DIYSynthMNL/Multi-Angle-Eurorack-1-Row-Case/images/Built 1.jpg

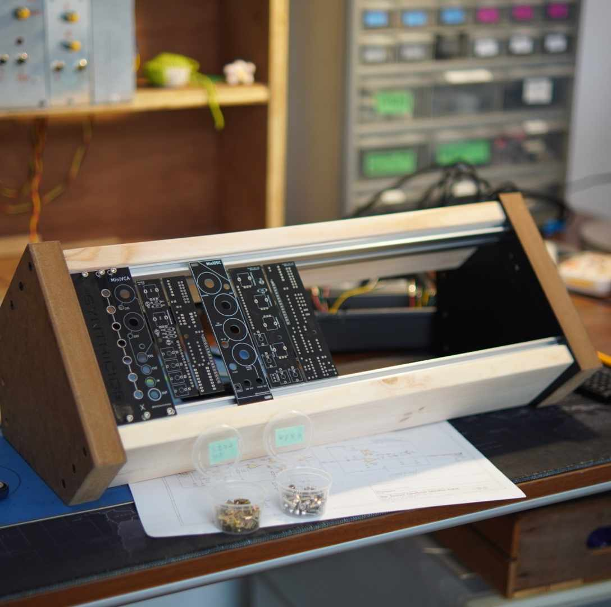
images/Built 1.jpg
