DIYSynthMNL/Multi-Angle-Eurorack-1-Row-Case/images/Built 4.jpg

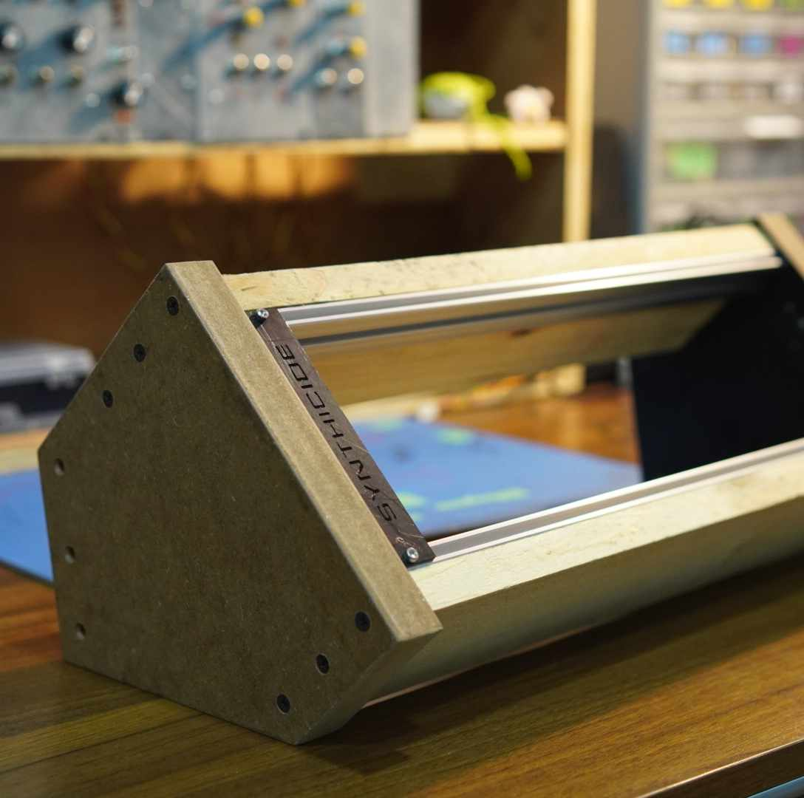
images/Built 4.jpg
