DIYSynthMNL/Multi-Angle-Eurorack-1-Row-Case/images/Built 5.jpg

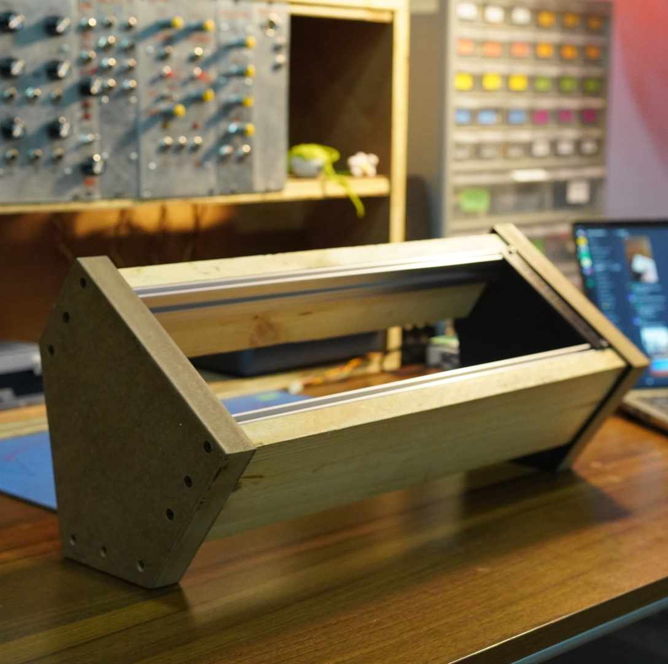
images/Built 5.jpg
