DIYSynthMNL/Multi-Angle-Eurorack-1-Row-Case/images/Built 6.jpg

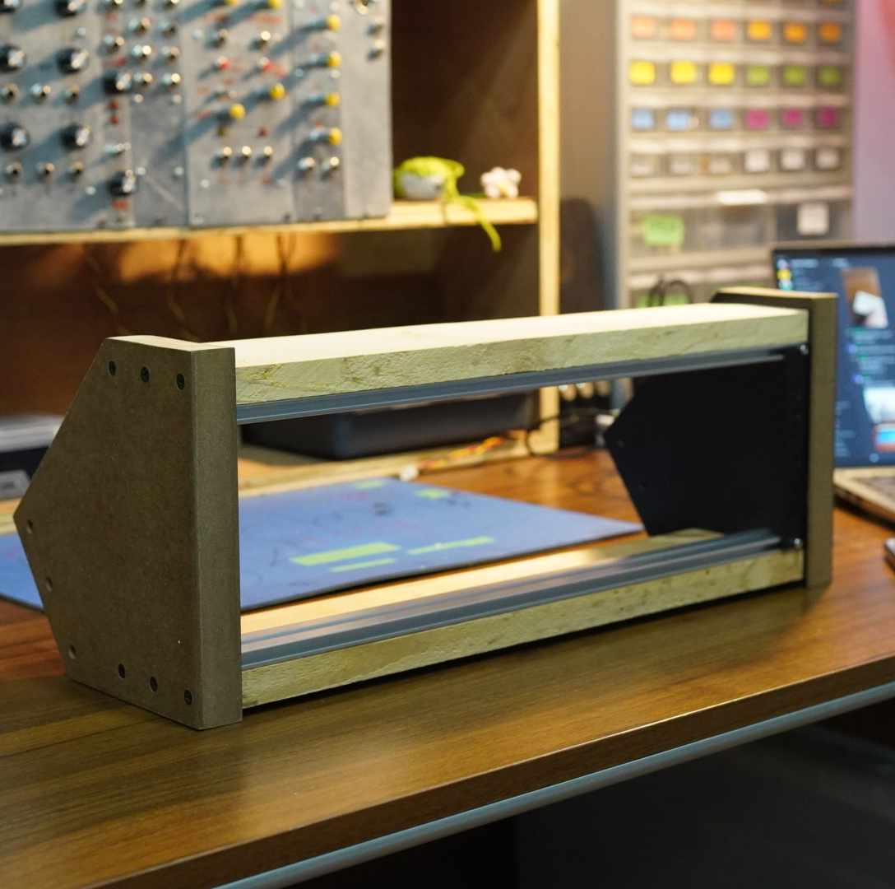
images/Built 6.jpg
