DIYSynthMNL/Multi-Angle-Eurorack-1-Row-Case/images/Untitled 1.png

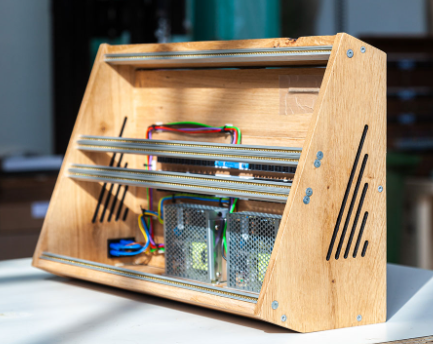
images/Untitled 1.png
