DIYSynthMNL/Multi-Angle-Eurorack-1-Row-Case/images/Untitled 3.png

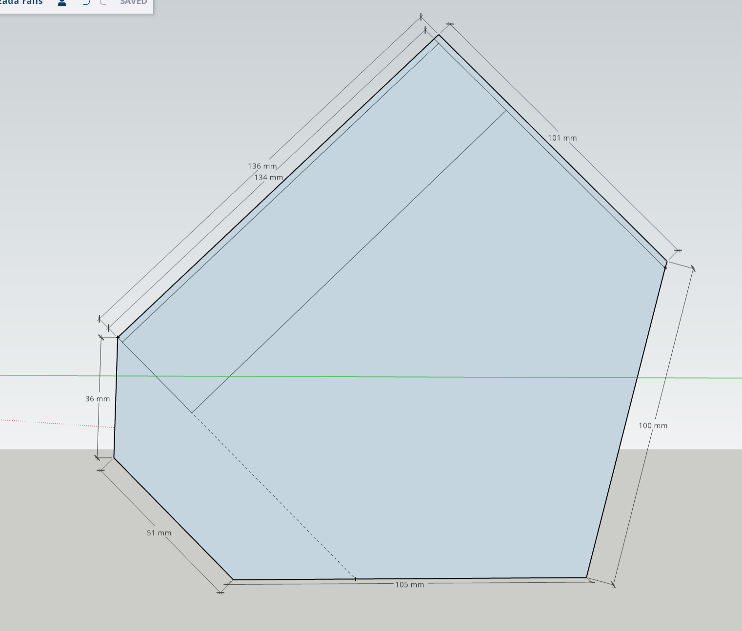
images/Untitled 3.png
