DIYSynthMNL/Multi-Angle-Eurorack-1-Row-Case/images/Untitled 6.png

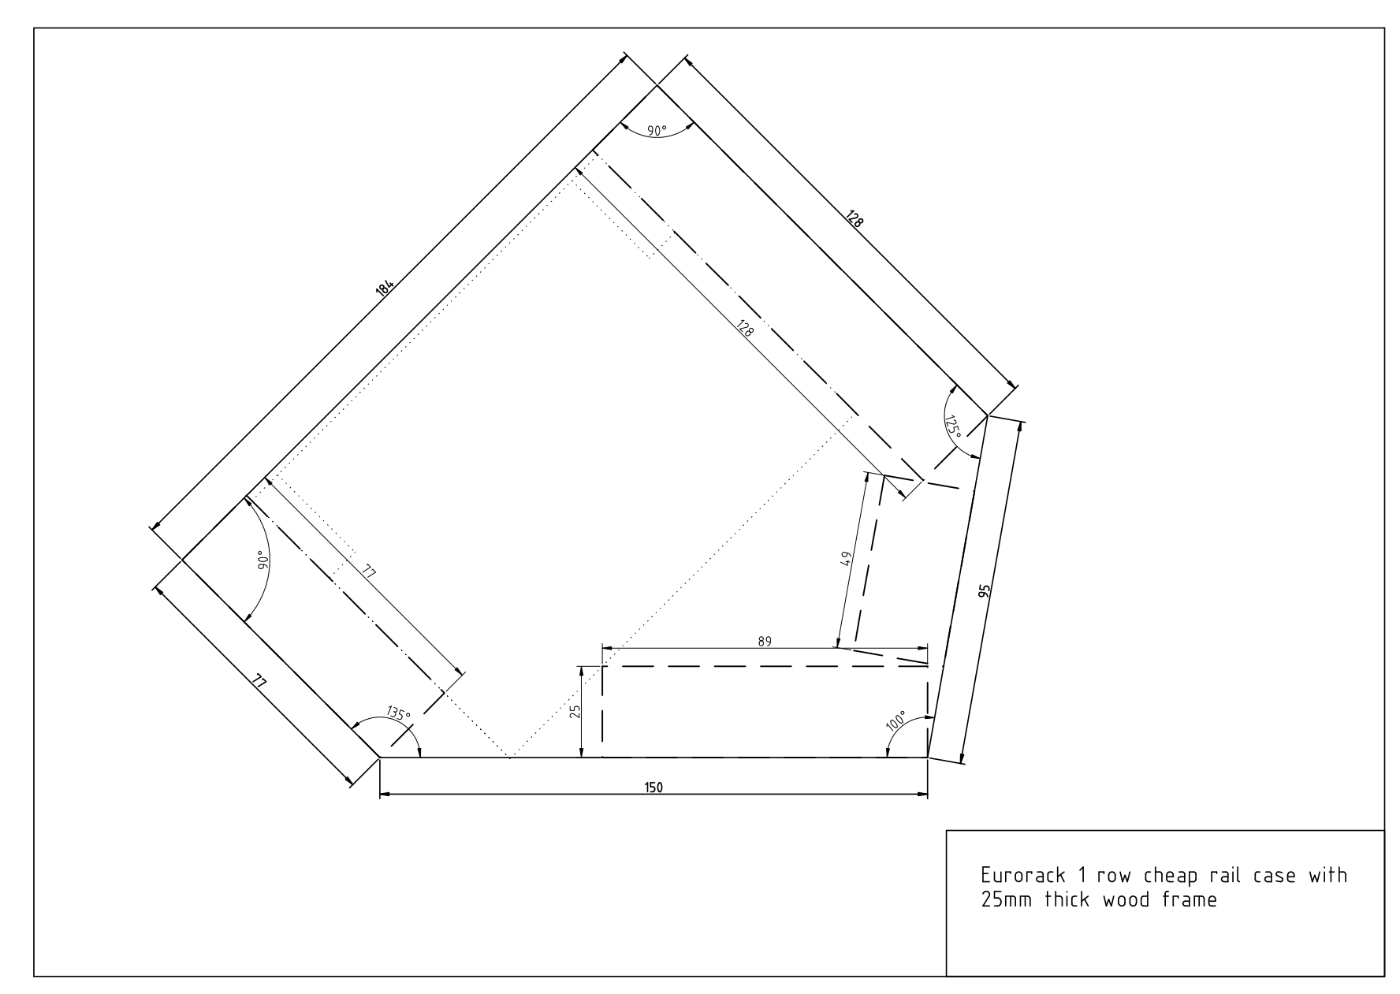
images/Untitled 6.png
