DIYSynthMNL/Multi-Angle-Eurorack-1-Row-Case/images/Untitled 8.png

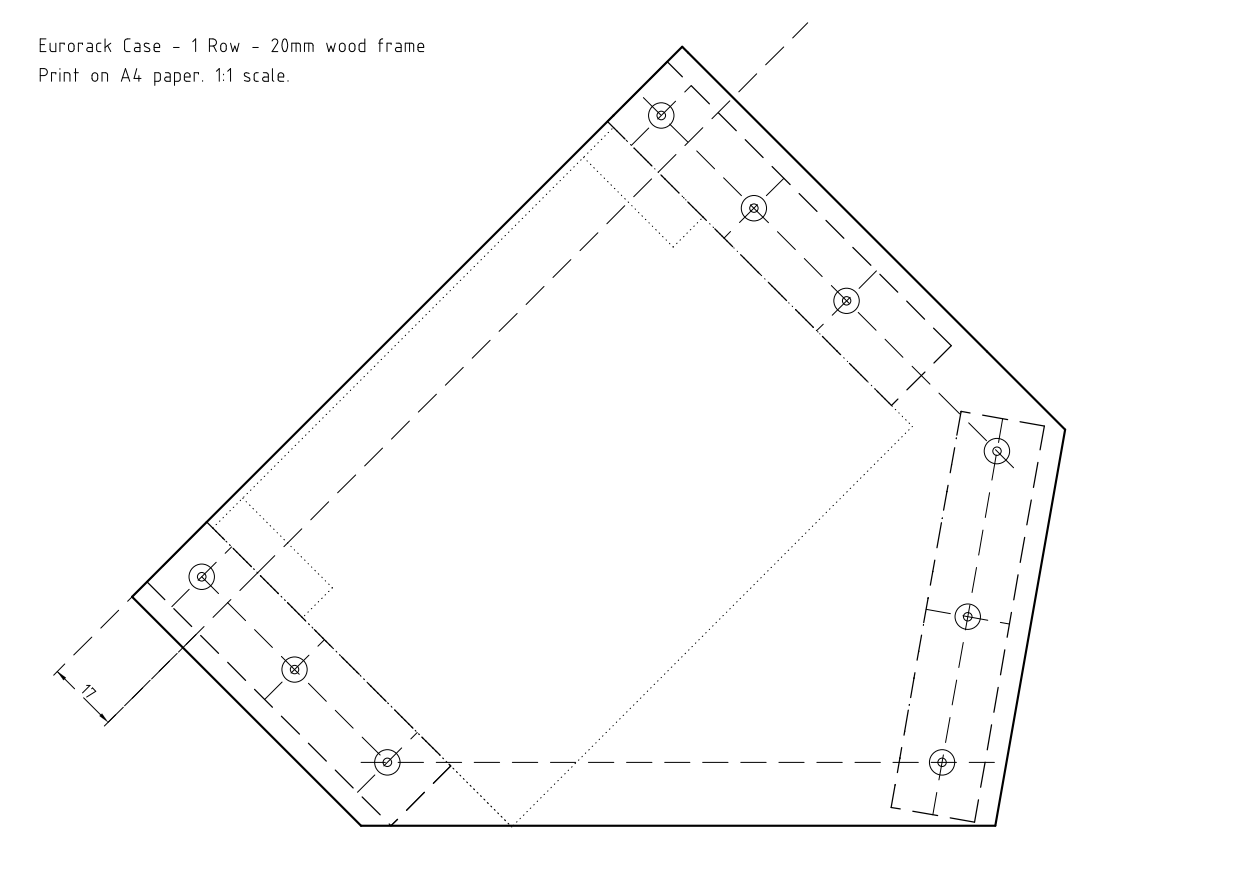
images/Untitled 8.png
