DIYSynthMNL/Multi-Angle-Eurorack-1-Row-Case/images/Untitled.png

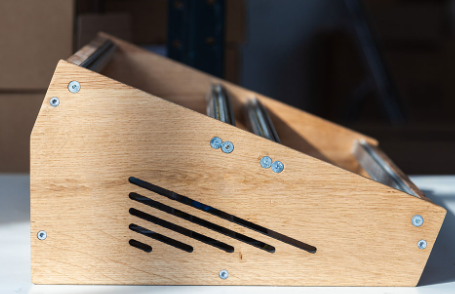
images/Untitled.png
