DIYSynthMNL/Multi-Angle-Eurorack-1-Row-Case/photos/with-modules-detail.jpg

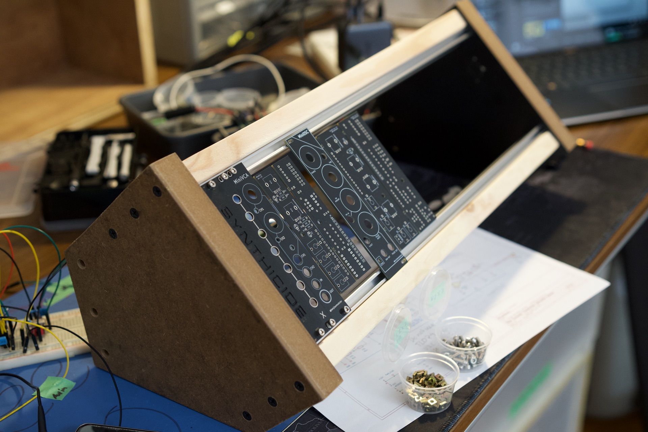
photos/with-modules-detail.jpg
