DIYSynthMNL/Multi-Angle-Eurorack-1-Row-Case/photos/with-modules.jpg

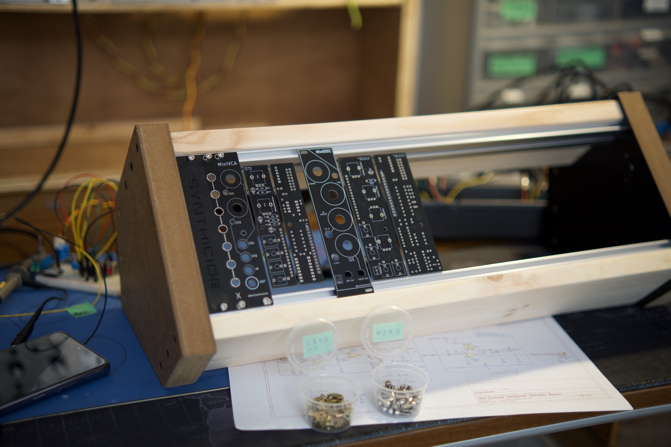
photos/with-modules.jpg
