DIYSynthMNL/Multi-Angle-Eurorack-1-Row-Case/photos/back-wiring.jpg

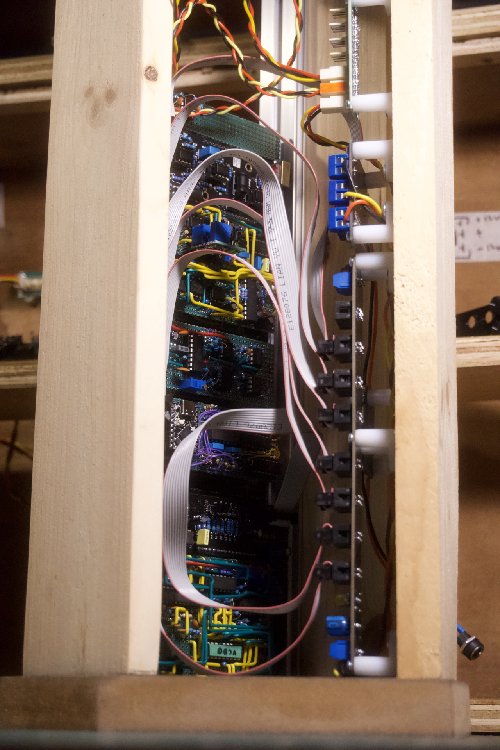
photos/back-wiring.jpg
