DIYSynthMNL/Multi-Angle-Eurorack-1-Row-Case/photos/build-1.jpg

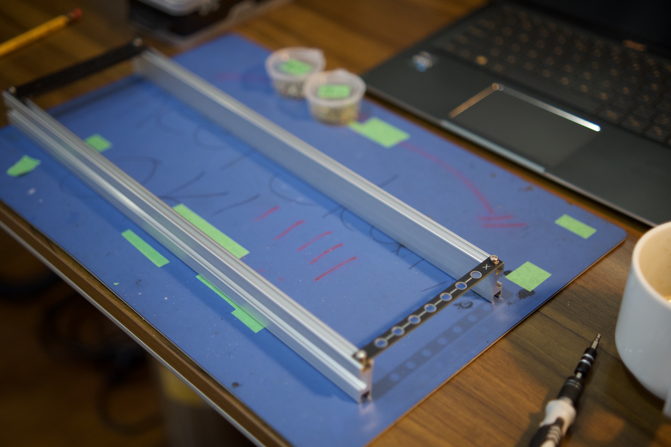
photos/build-1.jpg
