DIYSynthMNL/Multi-Angle-Eurorack-1-Row-Case/photos/build-2.jpg

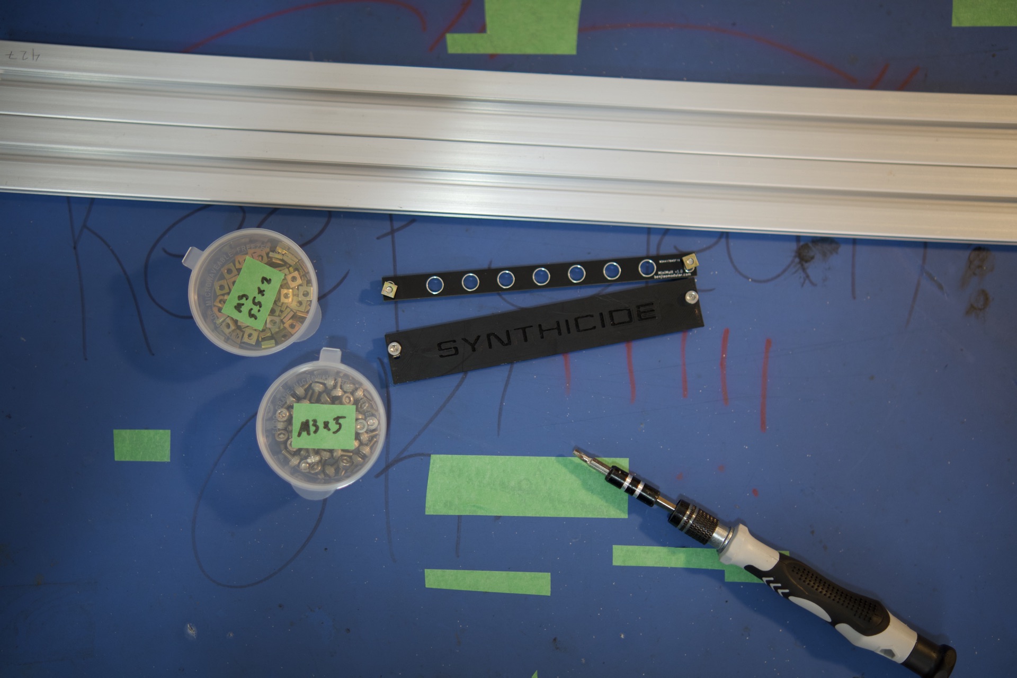
photos/build-2.jpg
