DIYSynthMNL/Multi-Angle-Eurorack-1-Row-Case/photos/build-3.jpg

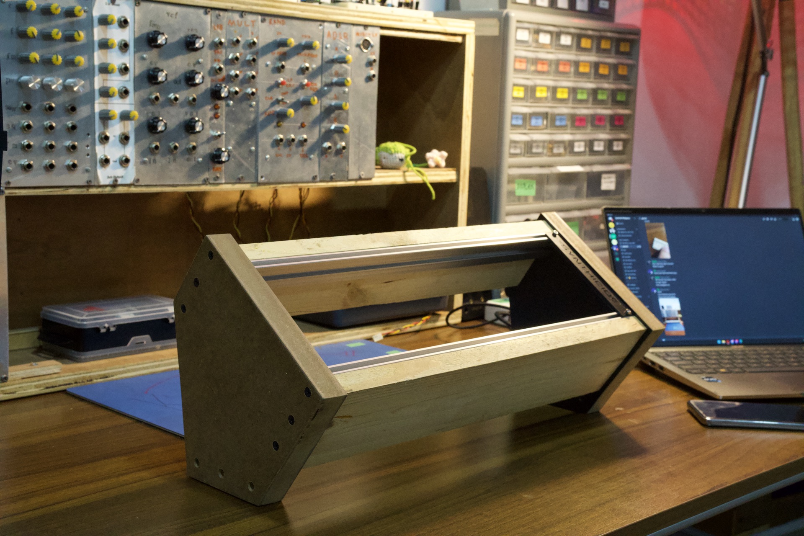
photos/build-3.jpg
