DIYSynthMNL/Multi-Angle-Eurorack-1-Row-Case/photos/build-4.jpg

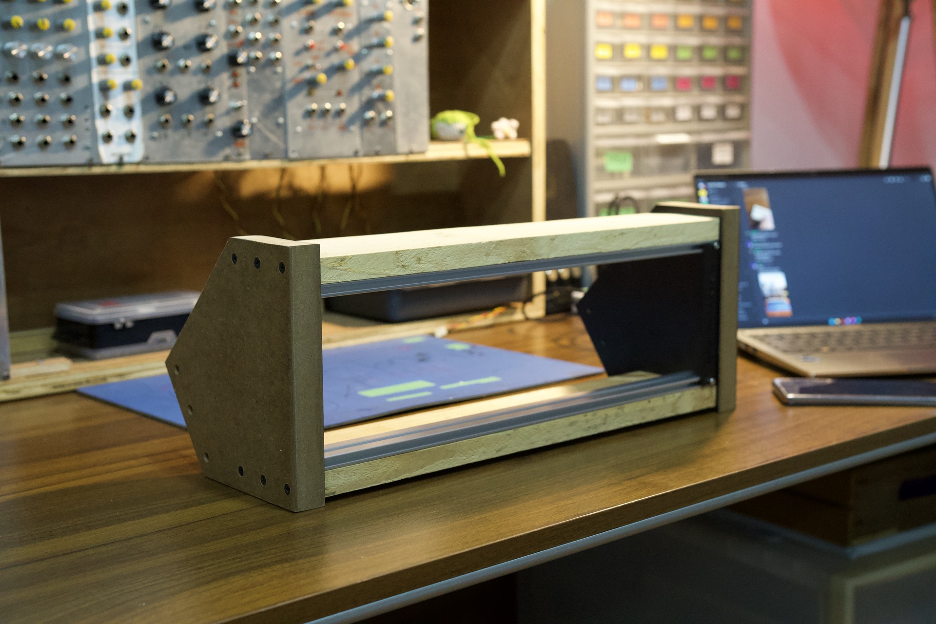
photos/build-4.jpg
